TeelSys/TeelSys_THL/Documentation/Images/cap01_01.png

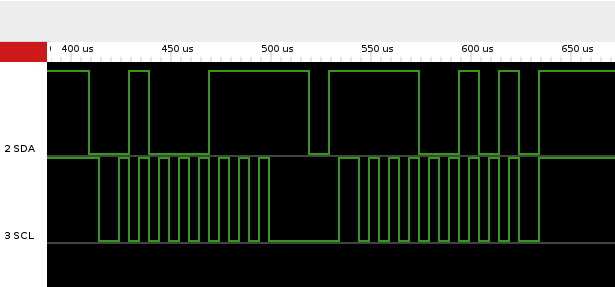
Documentation/Images/cap01_01.png
