TeelSys/TeelSys_THL/Documentation/Images/cap01_01b.png

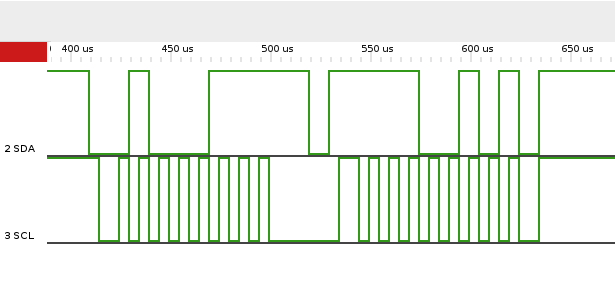
Documentation/Images/cap01_01b.png
