TeelSys/TeelSys_THL/Documentation/Images/cap01_02.png

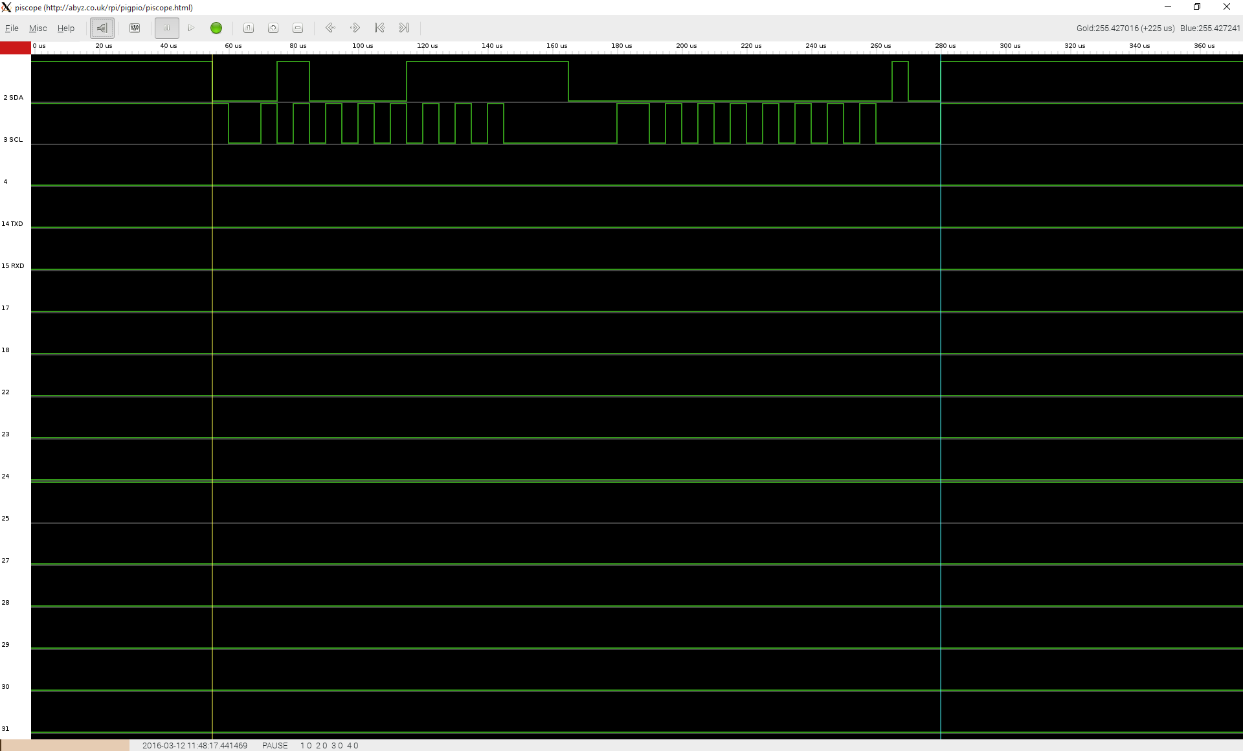
Documentation/Images/cap01_02.png
