TeelSys/TeelSys_THL/Documentation/Images/Memory Map.png

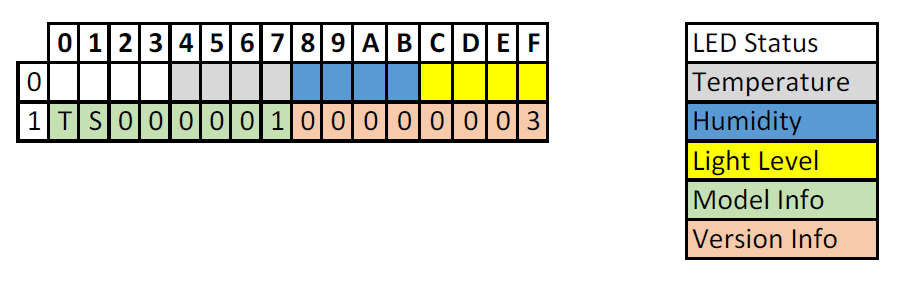
Documentation/Images/Memory Map.png
