TeelSys/TeelSys_THL/Documentation/Images/schema-1.png

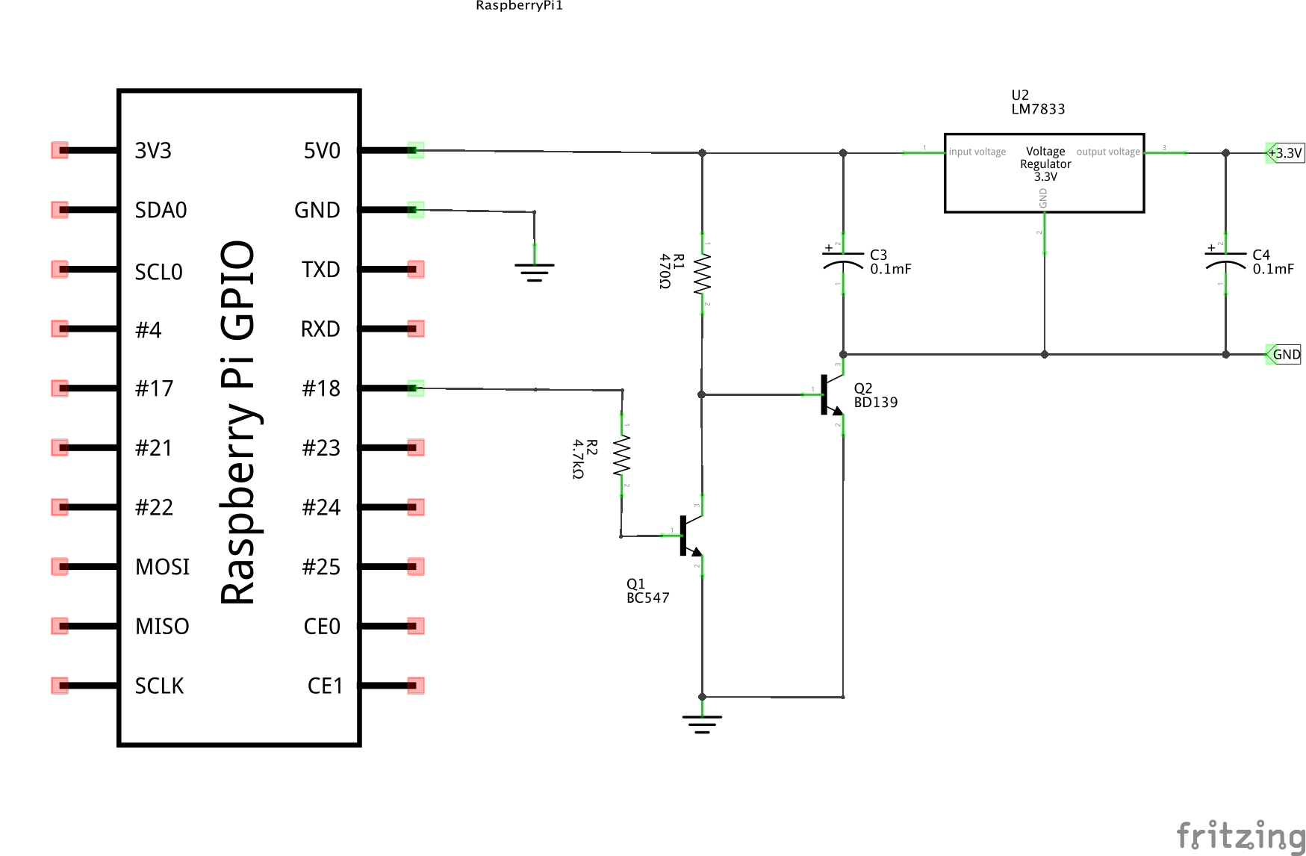
Documentation/Images/schema-1.png
