TeelSys/TeelSys_THL/Hardware/Fritzing/Step001_bb.png

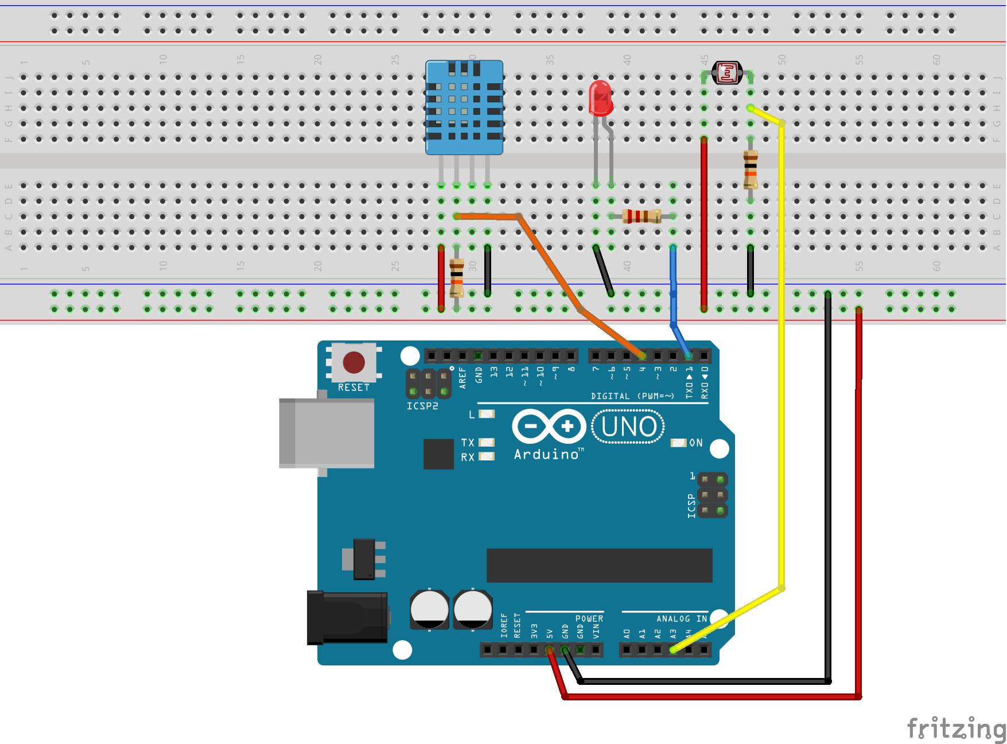
Hardware/Fritzing/Step001_bb.png
