TeelSys/TeelSys_THL/Hardware/Fritzing/Step001_schem.png

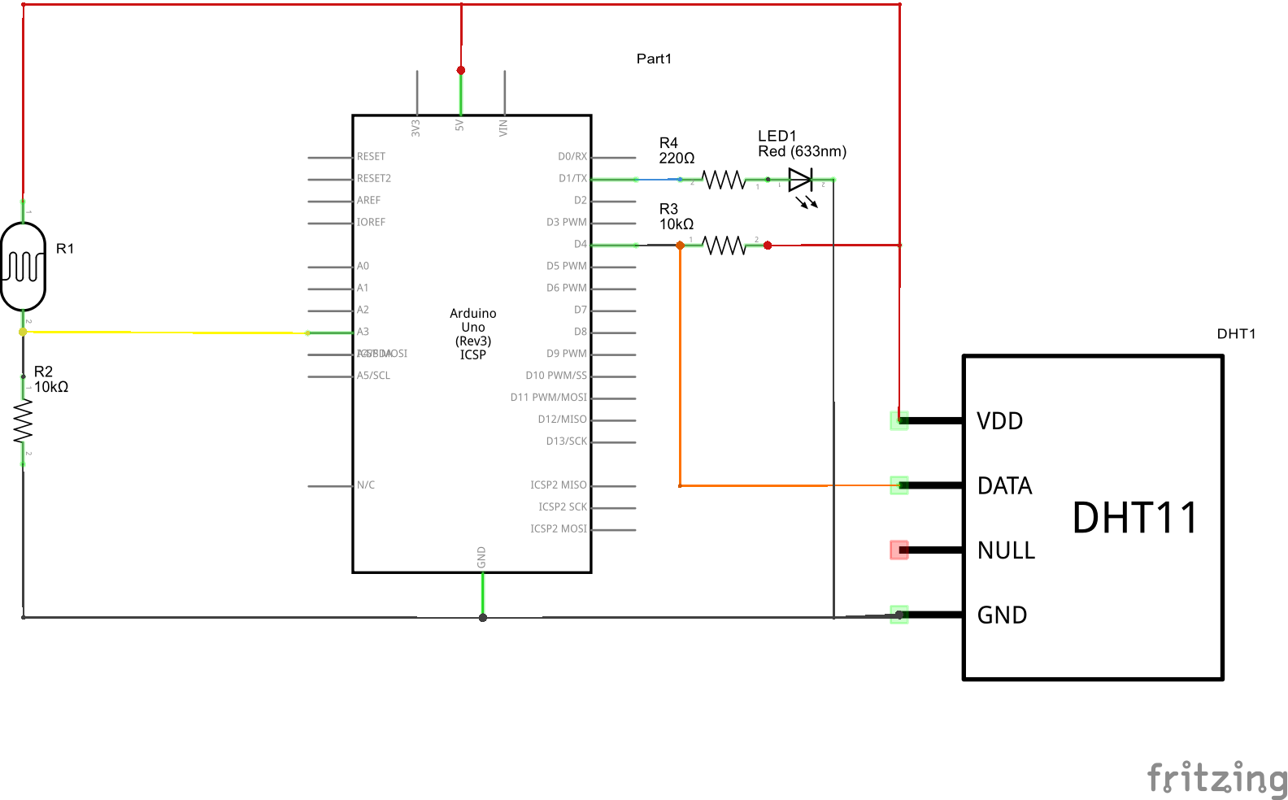
Hardware/Fritzing/Step001_schem.png
