TeelSys/TeelSys_THL/Hardware/Fritzing/Step002_bb.png

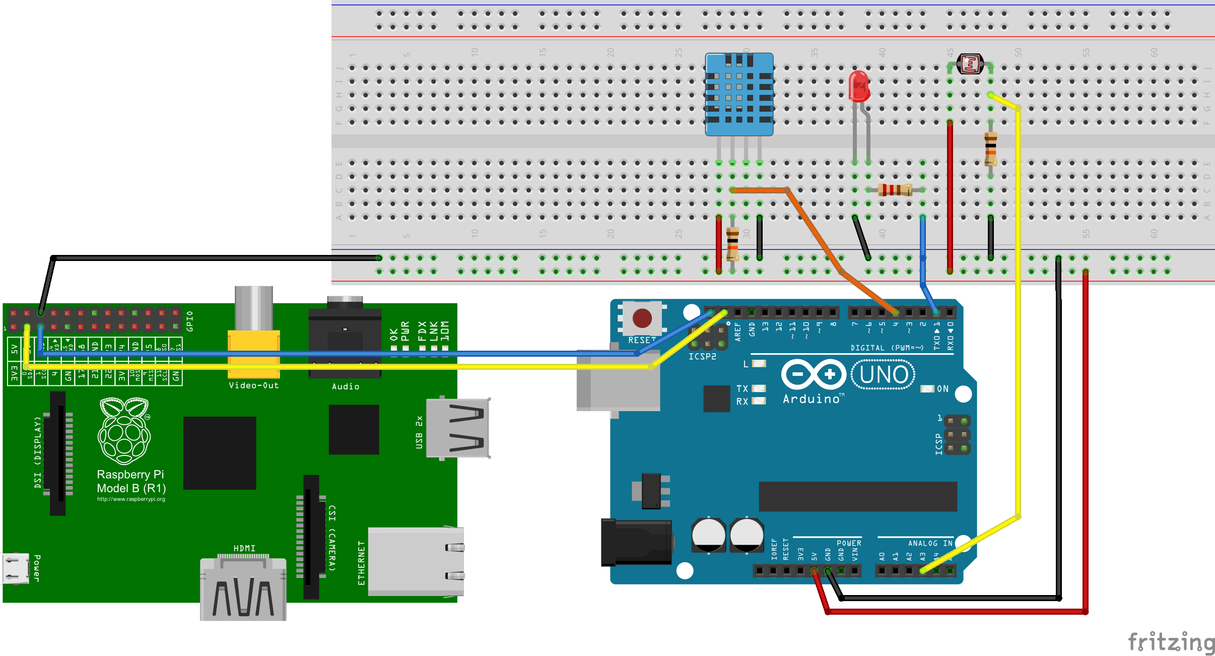
Hardware/Fritzing/Step002_bb.png
