TeelSys/TeelSys_THL/Hardware/Fritzing/Step002_schem.png

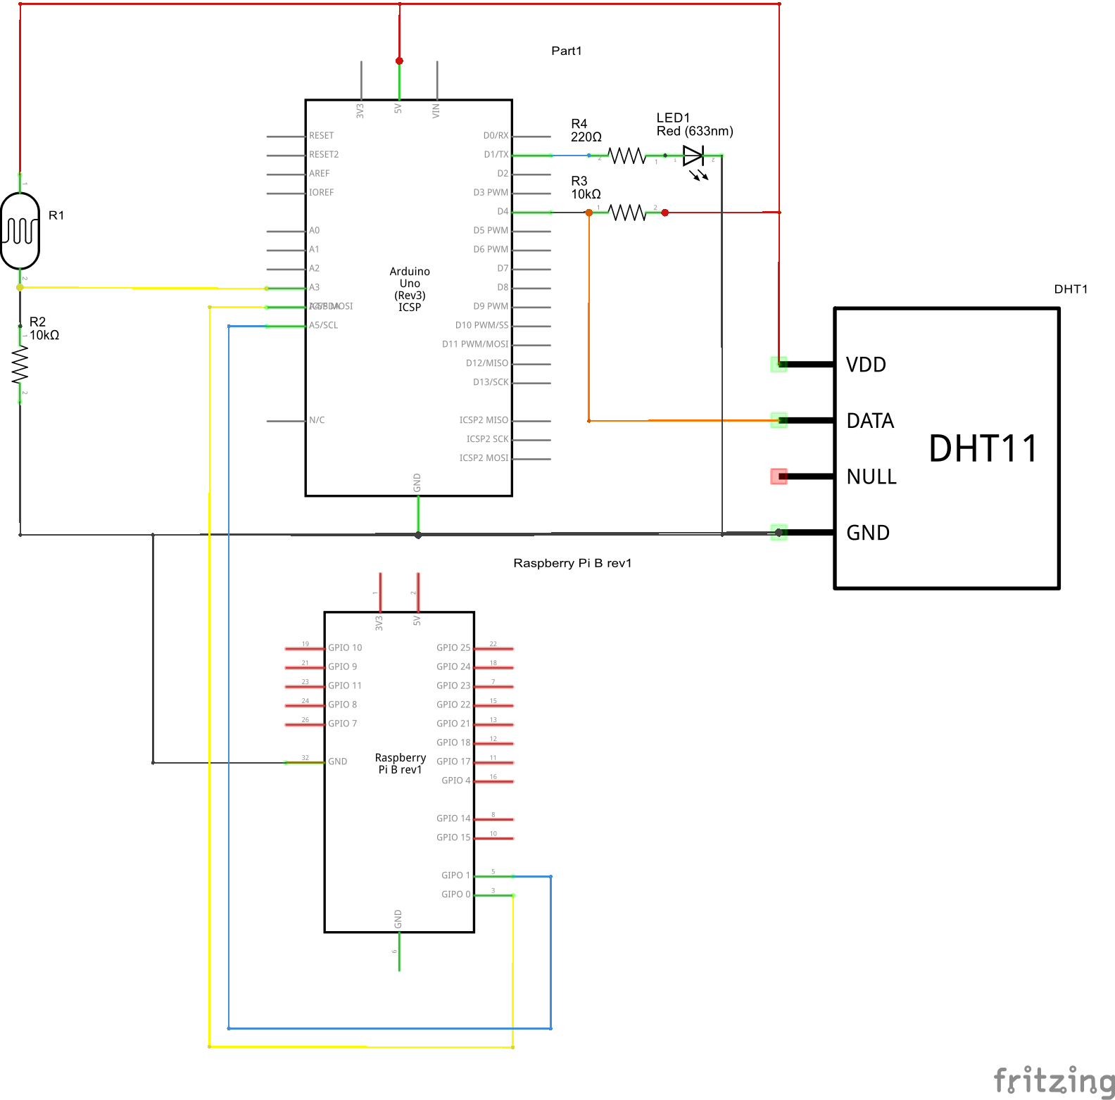
Hardware/Fritzing/Step002_schem.png
